envergokaycay/h-bridge-dc-ac-inverter/PCB/3D/DC-AC Inverter.jpg

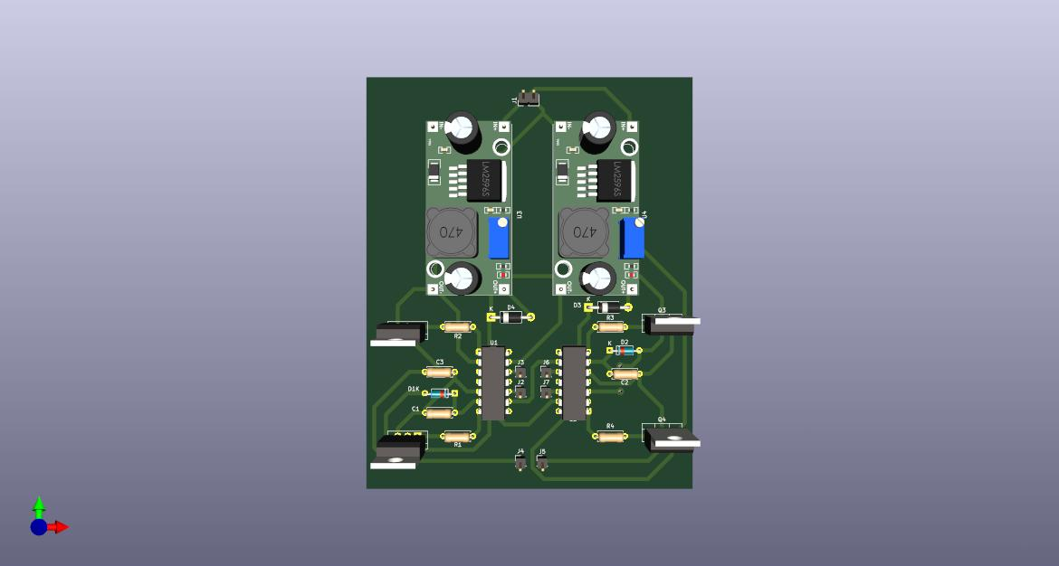
PCB/3D/DC-AC Inverter.jpg
