envergokaycay/h-bridge-dc-ac-inverter/Simulation Graphs/Output Graphs.jpg

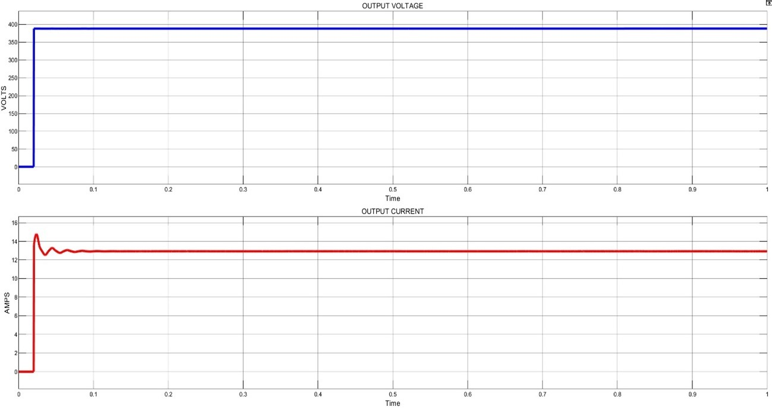
Simulation Graphs/Output Graphs.jpg
